ShawnHymel/wenk-sao/Images/board-avr-pocket-prgrammer.jpg

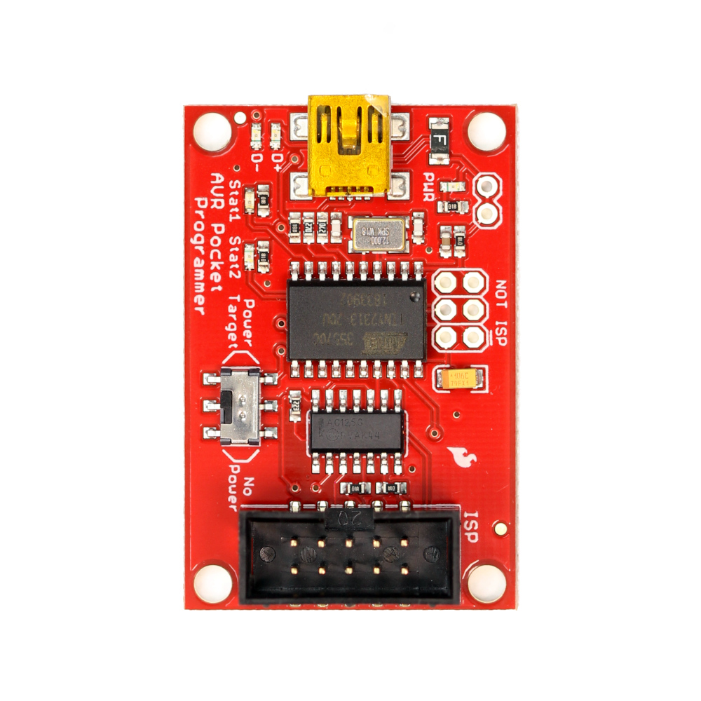
Images/board-avr-pocket-prgrammer.jpg
