ShawnHymel/wenk-sao/Images/gunter-back_sm_keepout.png

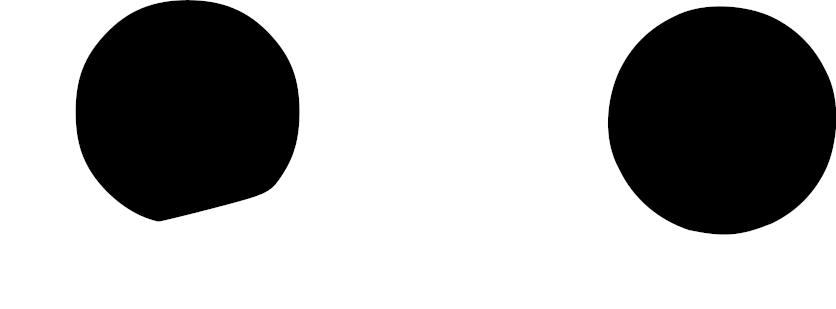
Images/gunter-back_sm_keepout.png
