ShawnHymel/wenk-sao/Images/gunter-outer.png

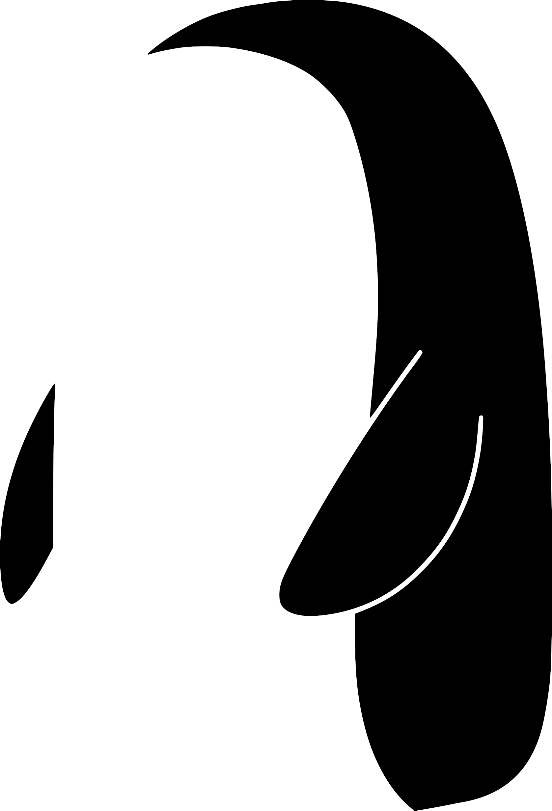
Images/gunter-outer.png
