ShawnHymel/wenk-sao/Images/gunter-silk.png

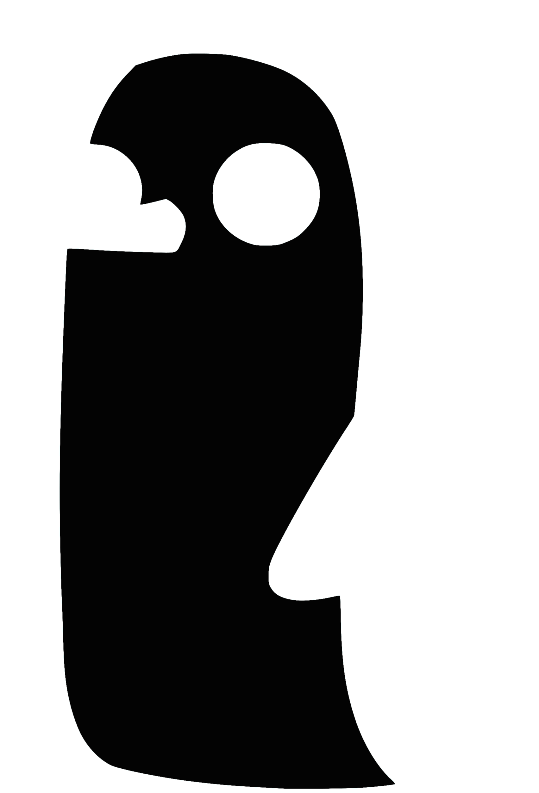
Images/gunter-silk.png
