ShawnHymel/wenk-sao/Images/gunter-sm_keepout.png

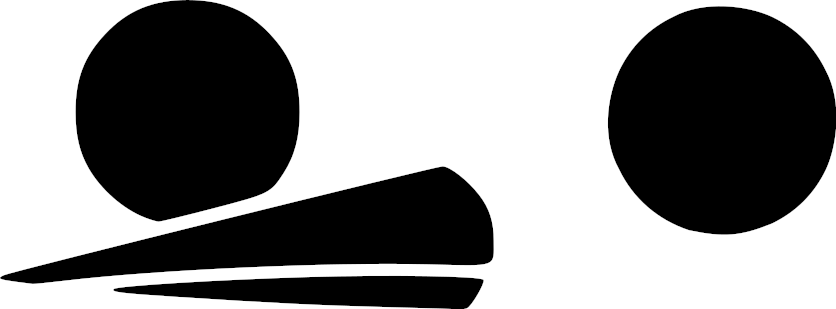
Images/gunter-sm_keepout.png
