ShawnHymel/wenk-sao/Images/programmer-hookup_bb.jpg

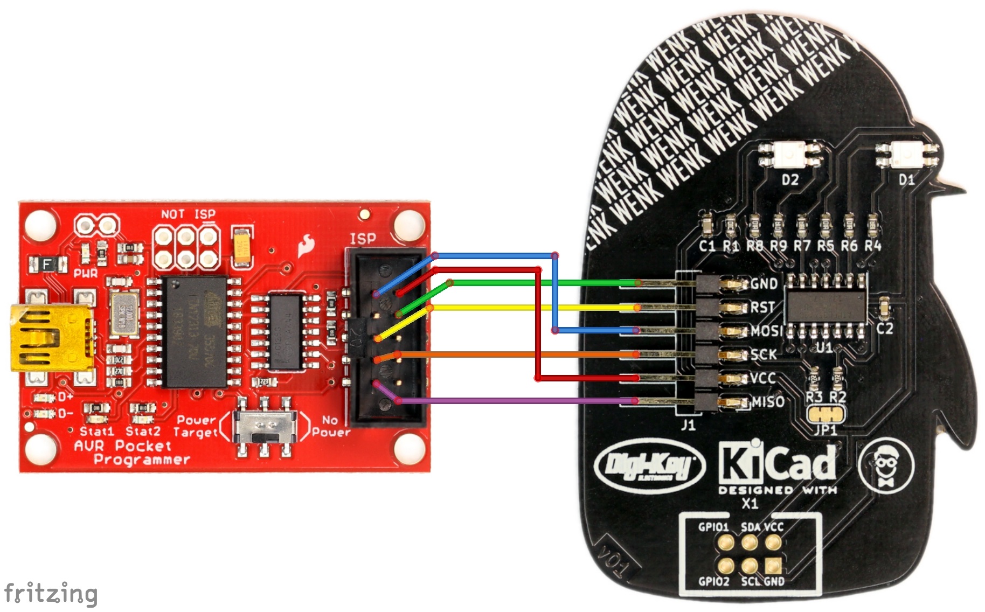
Images/programmer-hookup_bb.jpg
